mrginformal/Multiplexor/Images/2.jpg

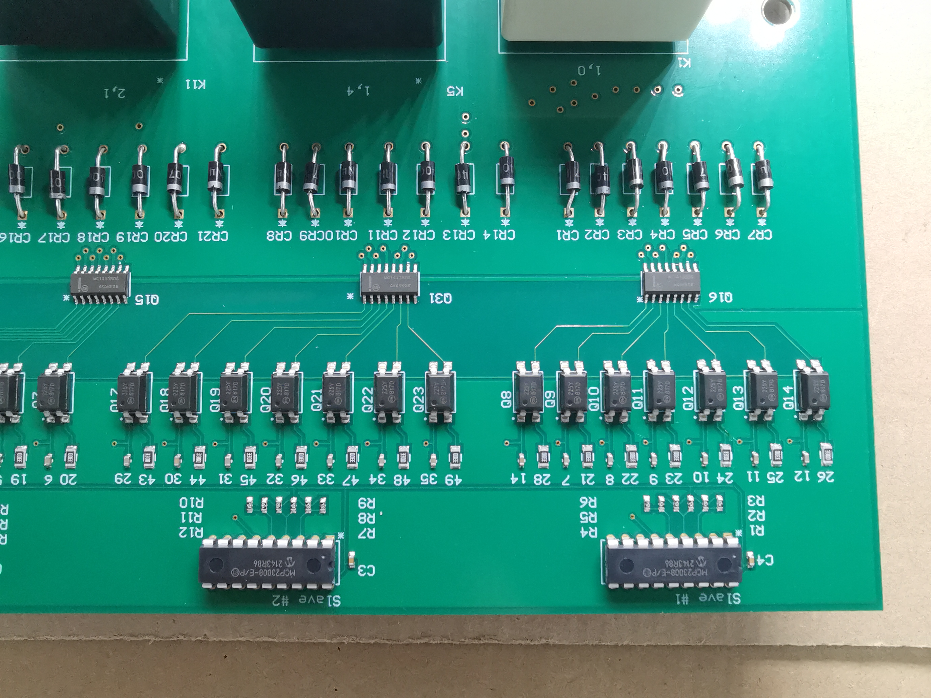
Images/2.jpg
