mrginformal/Multiplexor/Images/3.jpg

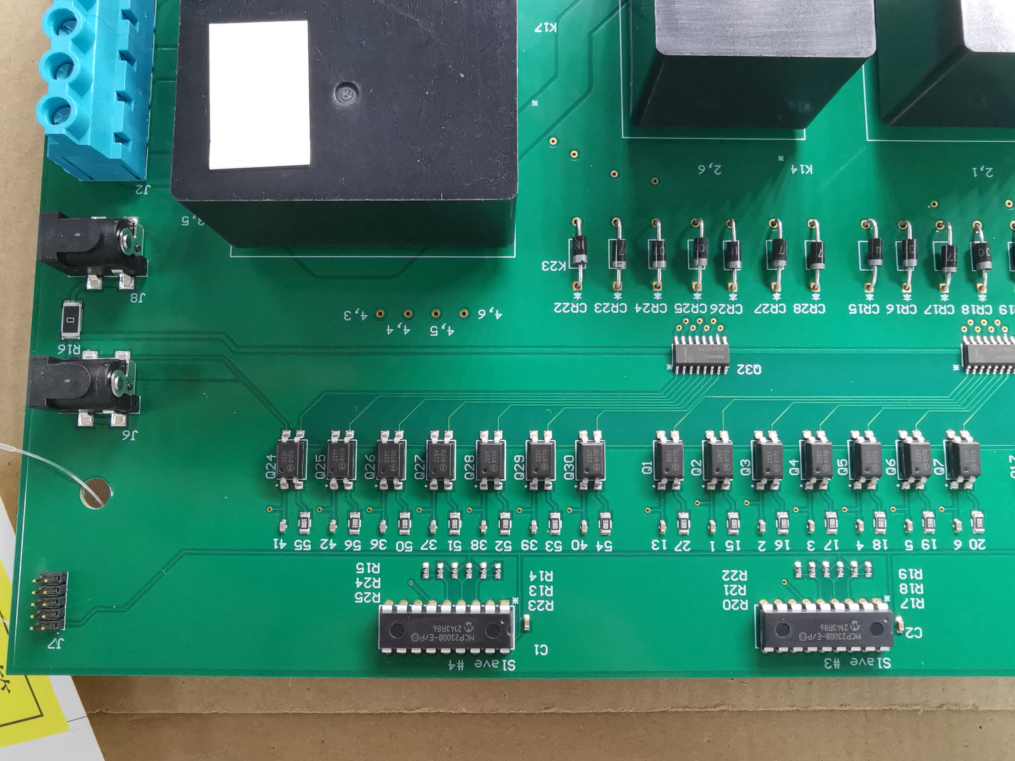
Images/3.jpg
