mrginformal/Multiplexor/Images/4.jpg

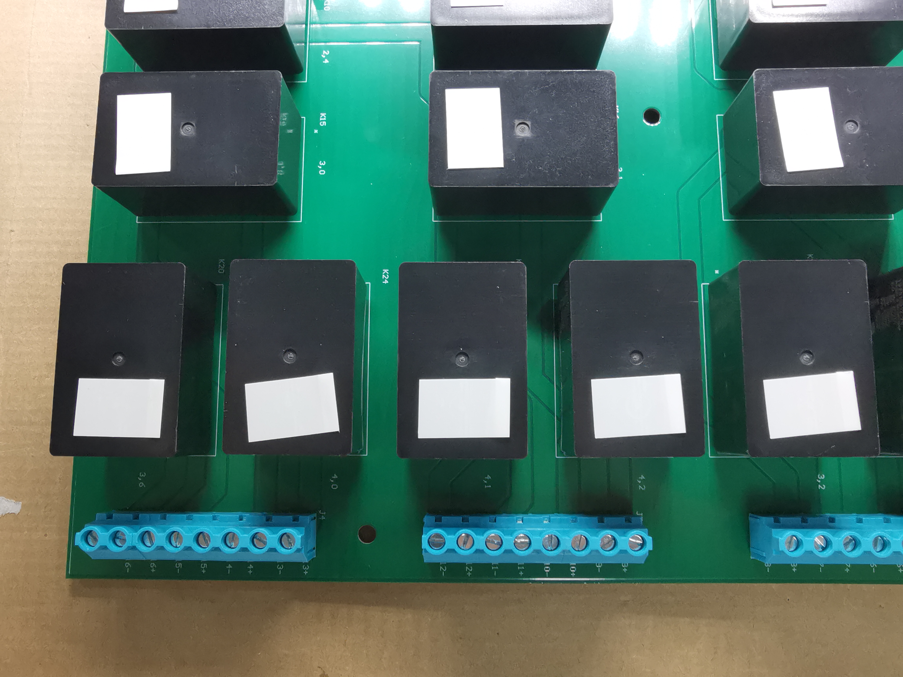
Images/4.jpg
