mrginformal/Multiplexor/Images/5.jpg

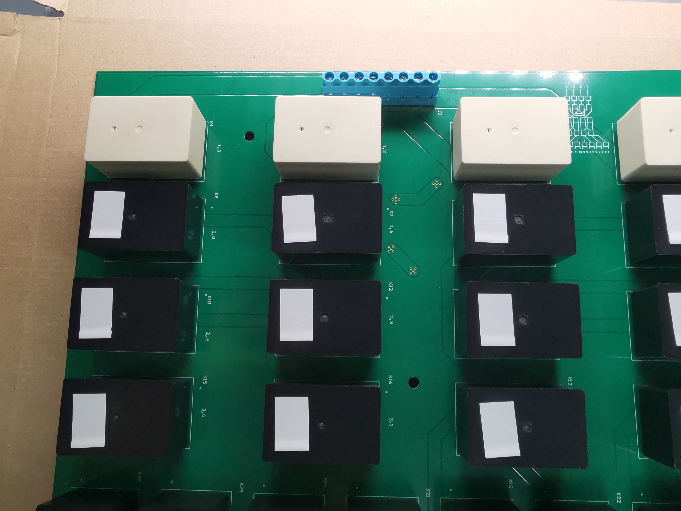
Images/5.jpg
